MarkD833/Arduino-SP0256-Shield/code/vocab_v1.1.asm

;====================================================================
; Arduino SP0256-AL2 Shield Project
; https://github.com/MarkD833/Arduino-SP0256-Shield
;====================================================================
; This is the lookup table that will provide the starting address
; in the EEPROM for the sequence of allophones required to speak
; the word or phrase.
;
; They are arranged with 5 words per row just to make it easier to
; count!
;
; The vocabulary is split into evenly spaced blocks of words so that
; all words starting with the same letter are grouped in the same block.
;
; For example, to speak the word DANGER, the index number is 751 and
; to speak the word INCHES, the index number is 2004.
;
; Feel free to alter the spacing but as it stands, you can have up to
; 250 words or phrases in each block.
;====================================================================

; 

;====================================================================
; Edit this text string to hold whatever identifier you want
;
VERSION_STR EQU "SP0256 Vocabulary v1.1"

    ORG 0000
    DW  VERSTR
    
; Words starting with A - index starts at 1

	DW	A,ABLE,ABORT,ABORTED,AC
	DW	ACCUMULATE,ACKNOWLEDGE,ACTIVATE,ACTIVATING,ACTIVE
	DW	ACTIVITY,ADD,ADDRESS,ADJUST,AFTER
	DW	AGAIN,AIR,AISLE,ALARM,ALERT
	DW	ALL,ALTERNATE,AM1,AM2,AMP
	DW	AMPERE,AN,AND,ANNOUNCEMENT,ANSWER
	DW	APRIL,ARRIVAL,ASK,ASSISTANCE,ASTERN
	DW	AT,ATTENTION,AUGUST,AUTHORIZE,AUTO
	DW	AVAILABLE,AVERAGE,AWAY

; Words starting with B - index starts at 250
	ORG	500
    DW	B,BACK,BAROMETRIC,BASEMENT,BATH
	DW	BATTERY,BEEN,BEFORE,BETWEEN,BIN
	DW	BLACK,BLOCKING,BLUE,BRAKE,BUDGET
	DW	BUDGETING,BUILDING,BUOY,BUSY,BUTTON
	DW	BUY,BY
	
; Words starting with C - index starts at 500
	ORG	1000
	DW	C,CALENDAR,CALL,CANCEL,CAPACITANCE
	DW	CAR,CASE,CAUTION,CEASE,CELSIUS
	DW	CENT,CENTI,CENTIGRADE,CENTIMETER,CHANGE
	DW	CHANNEL,CHECK,CHECKED,CHECKING,CIRCUIT
	DW	CLEAR,CLOCK,CLOSE,CLOSED,CODE
	DW	COLD,COLLIDE,COMMA,COMMAND,COMMON
	DW	COMMUNICATION,COMPLETE,COMPUTER,CONDITION,CONFIGURATION
	DW	CONNECT,CONTINUE,CONTROL,CONVERTER,COOKIE
	DW	COOL,COPY,CORRECT,COST,COUNT
	DW	CROSS,CUSTOMER,CUT,CUTTING
	
; Words starting with D - index starts at 750
	ORG	1500
	DW	D,DANGER,DATA,DATE,DAY
	DW	DC,DECEMBER,DECREASE,DEFAULT,DEGREE
	DW	DELAY,DEMONSTRATION,DEPOSIT,DEPTH,DIAL
	DW	DIALING,DID,DISABLE,DISABLED,DIVIDE
	DW	DOLLAR,DOOR,DOWN
	
; Words starting with E - index starts at 1000
	ORG	2000
	DW	E,EAST,EIGHT,EIGHTEEN,EIGHTY
	DW	ELECTRIC,ELECTRICITY,ELEVEN,ELSE,EMERGENCY
	DW	ENABLE,ENABLED,END,ENGAGE,ENTER
	DW	ENTRY,EQUAL,EQUALS,ERROR,ESCAPE
	DW	EVACUATE,EXAMINE,EXIT,EXTREME
	
; Words starting with F - index starts at 1250
	ORG	2500
	DW	F,FAIL,FAILED,FAILURE,FAR
	DW	FARAD,FAST,FASTER,FEBRUARY,FEET
	DW	FIFTEEN,FIFTH,FIFTY,FIGHT,FIRE
	DW	FIRST,FIVE,FLOOR,FLOW,FORTY
	DW	FORWARD,FOUR,FOURTEEN,FRIDAY,FROM
	DW	FRONTAL,FUEL,FUSE,FUSED
	
; Words starting with G - index starts at 1500
	ORG	3000
	DW	G,GALLON,GAS,GET,GO
	DW	GOING,GOOD,GRAM,GRAY,GREAT
	DW	GREATER,GREEN,GROUP
	
; Words starting with H - index starts at 1750
	ORG	3500
	DW	H,HALF,HAVE,HELLO,HELP
	DW	HERE,HERTZ,HIGH,HIGHER,HIRE
	DW	HIT,HOLD,HOME,HOUR,HOUSE
	DW	HUNDRED,HURT
	
; Words starting with I - index starts at 2000
	ORG	4000
	DW	I,IF,IN,INACTIVE,INCHES
	DW	INCORPORATED,INCORRECT,INCREASE,INSERT,INTERFACE
	DW	INTRUDER,INVALID,INVESTIGATE,IS,IT
	
; Words starting with J - index starts at 2250
	ORG	4500
	DW	J,JANUARY,JULY,JUNE,JUST
	
; Words starting with K - index starts at 2500
	ORG	5000
	DW	K,KEY,KEYPAD,KILO
	
; Words starting with L - index starts at 2750
	ORG	5500
	DW	L,LEAVE,LEFT,LESS,LESSER
	DW	LEVEL,LIE,LIGHT,LIME,LIMIT
	DW	LINE,LINK,LISTEN,LOAD,LOCK
	DW	LOCKED,LOOP,LOOPED,LOW,LOWER
	
; Words starting with M - index starts at 3000
	ORG	6000
	DW	M,MARCH,MARK,MAY,MEGA
	DW	MEMORY,MESSAGE,METER,MICRO,MILE
	DW	MILLI,MILLIMETER,MILLION,MINUS,MINUTE
	DW	MISS,MISSING,MODEL,MODEM,MODULE
	DW	MONDAY,MONITOR,MORE,MOVE,MY
	
; Words starting with N - index starts at 3250
	ORG	6500
	DW	N,NANO,NEAR,NEED,NEXT
	DW	NIGHT,NINE,NINETEEN,NINETY,NO
	DW	NORMAL,NORTH,NOT,NOTICE,NOVEMBER
	DW	NUMBER
	
; Words starting with O - index starts at 3500
	ORG	7000
	DW	O,OCLOCK,OCTOBER,OF,OFF
	DW	OHM,OKAY,ON,ONE,ONWARD
	DW	OPEN,OPERATOR,OPTICAL,OR_,OTHER
	DW	OUT,OVER,OVER_RANGE
	
; Words starting with P - index starts at 3750
	ORG	7500
	DW	P,PAIR,PAN,PARENTHESIS,PASS
	DW	PASSED,PAST,PER,PERCENT,PHONE
	DW	PHONE_NUMBER,PHYSICAL,PICO,PLACE,PLAY
	DW	PLEASE,PLUS,PM,POINT,POUND
	DW	POWER,PRESENT,PRESS,PRESSURE,PROGRAM
	DW	PULL,PULSE,PULSES,PUSH,PUT
	
; Words starting with Q - index starts at 4000
	ORG	8000
	DW	Q,QUARTER
	
; Words starting with R - index starts at 4250
	ORG	8500
	DW	R,RAIN,RANGE,RATE,RE
	DW	REACH,READY,RECEIVED,RECEIVER,RECORD
	DW	RED,REMOVE,REPAIR,REPEAT,REPLACE
	DW	RESET,RESISTANCE,RESPONSE,RESTORE,RESTORED
	DW	RETURN,REVERSE,RIGHT,RING,ROBOT
	DW	ROOM,ROUTE,RUN,RUNNING
	
; Words starting with S - index starts at 4500
	ORG	9000
	DW	S,SAFE,SATURDAY,SCORE,SECOND
	DW	SECURE,SECURITY,SEE,SELECT,SEND
	DW	SENSOR,SENT,SEPTEMBER,SEQUENCE,SERVICE
	DW	SET,SEVEN,SEVENTEEN,SEVENTY,SHORT
	DW	SHOULD,SIDE,SIGHT,SINK,SITE
	DW	SIX,SIXTEEN,SIXTY,SLOW,SLOWER
	DW	SMILE,SMOKE,SOUND,SOUTH,SPACE
	DW	SPAN,SPARE,SPEED,SPEAK,SPELL
	DW	SQUAD,STAIR,STAR,START,STARTING
	DW	STATION,STATUS,STEAM,STERN,STOP
	DW	STOPPED,STOPPING,STORE,STORM,STREAM
	DW	STREET,SUB,SUBSCRIBER,SUNDAY,SUPERVISORY
	DW	SWITCH,SWITCHED,SYSTEM
	
; Words starting with T - index starts at 4750
	ORG	9500
	DW	T,TALK,TALKING,TANK,TAPE
	DW	TAPING,TARGET,TEA,TEAR,TEEN
	DW	TEMPERATURE,TEMPORARY,TEN,TERMINATE,TERMINATED
	DW	TEST,THAN,THANK,THANKYOU,THAT
	DW	THE,THEE,THEN,THERE,THERM
	DW	THERMAL,THIRD,THIRTEEN,THIRTY,THIS
	DW	THOUSAND,THREE,THURSDAY,TIDE,TIME
	DW	TIP,TODAY,TONE,TOTAL,TOUCH
	DW	TRACKING,TRAFFIC,TRANSFER,TRIP,TRUE
	DW	TRUNK,TRY,TUESDAY,TURN,TWELVE
	DW	TWENTY,TWO,TYPE
	
; Words starting with U - index starts at 5000
	ORG	10000
	DW	U,UN,UNABLE,UNATTENDED,UNIT
	DW	UNKNOWN,UNLOCK,UNLOCKED,UNTRUE,UP
	DW	USE,USED,UTILITY
	
; Words starting with V - index starts at 5250
	ORG	10500
	DW	V,VOICE,VOLT,VOLTAGE,VOTE
	
; Words starting with W - index starts at 5500
	ORG	11000
	DW	W,WAIT,WAITING,WAKE,WAKEUP
	DW	WARM,WARNING,WAS,WATER,WATT
	DW	WAVE,WEAR,WEDNESDAY,WEEK,WELCOME
	DW	WEST,WHAT,WILL,WIND1,WIND2
	DW	WISH,WITH,WITHIN,WORD,WORK
	DW	WORKING
	
; Words starting with X - index starts at 5750
	ORG	11500
	DW	X,XRAY
	
; Words starting with Y - index starts at 6000
	ORG	12000
	DW	Y,YELLOW,YES,YOU,YOUR
	
; Words starting with Z - index starts at 6250
	ORG	12500
	DW	Z,ZERO,ZONE

;====================================================================
; Version string from the start of this file will get stored here
;====================================================================
VERSTR:
    DB  VERSION_STR,0
    
;====================================================================
; These are the sequences of allophones needed to create the sound
; of each individual word. Make sure to end each sequence with 0xFF
;
; The words (i.e. labels) do not need to be in alphabetical order. 
;====================================================================

A:		DB	PA2,EY,PA3,0xFF
ABLE:		DB	PA2,EY,PA2,BB2,EL,PA3,0xFF
ABORT:		DB	PA2,AX,PA2,BB2,OR,PA3,TT2,PA3,0xFF
ABORTED:		DB	PA2,AX,PA2,BB2,OR,PA3,TT2,IH,PA2,DD1,PA3,0xFF
AC:		DB	PA2,EY,PA3,SS,SS,IY,PA3,0xFF		; Alternating Current
ACCUMULATE:		DB	PA2,AE,PA3,KK1,YY1,UW1,MM,YY1,UW1,LL,EY,PA3,TT2,PA3,0xFF
ACKNOWLEDGE:		DB	PA2,AE,PA3,KK2,NN1,OW,LL,EH,PA2,JH,PA3,0xFF
ACTIVATE:		DB	PA2,AE,PA3,KK1,PA3,TT2,IH,VV,EY,PA3,TT2,PA3,0xFF
ACTIVATING:		DB	PA2,AE,PA3,KK1,PA3,TT2,IH,VV,EY,PA3,TT2,IH,NG,PA3,0xFF
ACTIVE:		DB	PA2,AE,PA3,KK1,PA3,TT2,IH,VV,PA3,0xFF
ACTIVITY:		DB	PA2,AE,PA3,KK1,PA3,TT2,IH,VV,IH,PA3,TT2,IY,PA3,0xFF
ADD:		DB	PA2,AE,AE,PA2,DD1,PA3,0xFF
ADDRESS:		DB	PA2,AE,PA2,DD2,RR2,EH,SS,PA3,0xFF
ADJUST:		DB	PA2,AE,PA2,JH,AX,SS,SS,PA3,TT2,PA3,0xFF
AFTER:		DB	PA2,AE,FF,PA3,TT2,ER1,PA3,0xFF
AGAIN:		DB	PA2,AX,PA2,GG1,EH,EH,NN1,PA3,0xFF
AIR:		DB	PA2,EH,XR,PA3,0xFF
AISLE:		DB	PA2,AY,EL,PA3,0xFF
ALARM:		DB	PA2,AX,LL,AR,MM,PA3,0xFF
ALERT:		DB	PA2,AX,LL,ER1,PA3,TT2,PA3,0xFF
ALL:		DB	PA2,AO,LL,PA3,0xFF
ALTERNATE:		DB	PA2,AO,LL,PA3,TT2,ER1,NN1,EY,PA3,TT2,PA3,0xFF
AM1:		DB	PA2,AE,MM,PA3,0xFF			; AM - as in I AM
AM2			DB	PA2,EY,PA3,EH,EH,MM,PA3,0xFF	; A.M. - time
AMP:		DB	PA2,AE,MM,PA1,PP,PA3,0xFF
AMPERE:		DB	PA2,AE,MM,PA3,PP,ER1,PA3,0xFF
AN:		DB	PA2,AE,NN1,PA3,0xFF
AND:		DB	PA2,AE,NN1,PA2,DD1,PA3,0xFF
ANNOUNCEMENT:		DB	PA2,AE,NN1,AW,NN1,SS,SS,MM,IH,NN1,PA3,TT2,PA3,0xFF
ANSWER:		DB	PA2,AE,NN1,SS,SS,ER1,PA3,0xFF
APRIL:		DB	PA2,AX,PA3,PP,RR2,IH,LL,PA3,0xFF
ARRIVAL:		DB	PA2,AX,RR2,AY,VV,EL,PA3,0xFF
ASK:		DB	PA2,AE,SS,SS,PA3,KK2,PA3,0xFF
ASSISTANCE:		DB	PA2,AE,SS,SS,IH,SS,SS,PA3,TT2,AE,NN1,SS,SS,PA3,0xFF
ASTERN:		DB	PA2,AE,SS,SS,PA3,TT2,ER1,PA2,NN1,PA3,0xFF
AT:		DB	PA2,AE,PA3,TT2,PA3,0xFF
ATTENTION:		DB	PA2,AE,PA3,TT2,EH,NN1,SH,AX,NN1,PA3,0xFF
AUGUST:		DB	PA2,AO,PA2,GG2,AX,SS,SS,PA3,TT2,PA3,0xFF
AUTHORIZE:		DB	PA2,AO,TH,ER1,AY,PA2,ZZ,PA3,0xFF
AUTO:		DB	PA2,AO,PA3,TT2,OW,PA3,0xFF
AVAILABLE:		DB	PA2,AX,VV,EY,LL,AX,PA2,BB2,EL,PA3,0xFF
AVERAGE:		DB	PA2,AX,VV,ER1,IH,PA2,JH,PA3,0xFF
AWAY:		DB	PA2,AX,WW,EY,PA3,0xFF
B:		DB	PA2,BB2,IY,PA3,0xFF
BACK:		DB	PA2,BB2,AE,PA3,KK2,PA3,0xFF
BAROMETRIC:		DB	PA2,BB2,XR,AX,MM,EH,PA3,TT2,RR2,IH,PA3,KK2,PA3,0xFF
BASEMENT:		DB	PA2,BB2,EY,SS,MM,IH,NN1,PA3,TT2,PA3,0xFF
BATH:		DB	PA2,BB2,AE,TH,PA3,0xFF
BATTERY:		DB	PA2,BB2,AE,PA3,TT2,ER1,IY,PA3,0xFF
BEEN:		DB	PA2,BB2,IY,NN1,PA3,0xFF
BEFORE:		DB	PA2,BB2,IY,FF,OR,PA3,0xFF
BETWEEN:		DB	PA2,BB2,IY,TT2,WW,IY,NN1,PA3,0xFF
BIN:		DB	PA2,BB2,IH,NN1,PA3,0xFF
BLACK:		DB	PA2,BB1,LL,AE,PA3,KK2,PA3,0xFF
BLOCKING:		DB	PA2,BB1,LL,AA,PA3,KK1,IH,NG,PA3,0xFF
BLUE:		DB	PA2,BB1,LL,UW2,PA3,0xFF
BRAKE:		DB	PA2,BB1,RR2,EY,PA3,KK1,PA3,0xFF
BUDGET:		DB	PA2,BB2,AX,PA2,JH,EH,PA3,TT2,PA3,0xFF
BUDGETING:		DB	PA2,BB2,AX,PA2,JH,EH,PA3,TT2,IH,NG,PA3,0xFF
BUILDING:		DB	PA2,BB2,IH,IH,LL,PA2,DD2,IH,NG,PA3,0xFF
BUOY:		DB	PA2,BB2,OY,PA3,0xFF
BUSY:		DB	PA2,BB2,IH,ZZ,IY,PA3,0xFF
BUTTON:		DB	PA2,BB2,AX,PA3,TT2,AX,NN1,PA3,0xFF
BUY:		DB	PA2,BB2,AY,PA3,0xFF
BY:		DB	PA2,BB2,AY,PA3,0xFF
C:		DB	PA2,SS,SS,IY,PA3,0xFF
CALENDAR:	DB	PA2,KK1,AE,LL,EH,NN1,PA2,DD2,ER1,PA3,0XFF
CALL:		DB	PA2,KK1,AO,LL,PA3,0xFF
CANCEL:		DB	PA2,KK1,AE,NN1,SS,SS,EL,PA3,0xFF
CAPACITANCE:		DB	PA2,KK1,AE,PA3,PP,AE,SS,SS,IH,PA3,TT2,AE,NN1,SS,SS,PA3,0xFF
CAR:		DB	PA2,KK3,AR,PA3,0xFF
CASE:		DB	PA2,KK1,EY,SS,PA3,0xFF
CAUTION:		DB	PA2,KK1,AO,SH,AX,NN1,PA3,0xFF
CEASE:		DB	PA2,SS,SS,IY,ZZ,PA3,0xFF
CELSIUS:		DB	PA2,SS,SS,EH,LL,SS,SS,IH,AX,ZZ,PA3,0xFF
CENT:		DB	PA2,SS,SS,EH,NN1,PA3,TT2,PA3,0xFF
CENTI:		DB	PA2,SS,SS,EH,NN1,PA3,TT2,IY,PA3,0xFF
CENTIGRADE:		DB	PA2,SS,SS,EH,NN1,PA3,TT2,IH,PA2,GG2,RR2,EY,PA2,DD2,PA3,0xFF
CENTIMETER:		DB	PA2,SS,SS,EH,NN1,PA3,TT2,IH,MM,IY,PA3,TT2,ER1,PA3,0xFF
CHANGE:		DB	PA2,CH,EY,NN1,PA2,JH,PA3,0xFF
CHANNEL:		DB	PA2,PA3,CH,AE,NN2,EL,PA3,0xFF
CHECK:		DB	PA2,CH,EH,PA3,KK2,PA3,0xFF
CHECKED:		DB	PA2,CH,EH,PA3,KK2,PA2,TT2,PA3,0xFF
CHECKING:		DB	PA2,CH,EH,PA3,KK1,IH,NG,PA3,0xFF
CIRCUIT:		DB	PA2,SS,SS,ER2,PA3,KK3,IH,PA3,TT2,PA3,0xFF
CLEAR:		DB	PA2,KK1,LL,YR,PA3,0xFF
CLOCK:		DB	PA2,KK1,LL,AA,PA3,KK2,PA3,0xFF
CLOSE:		DB	PA2,KK1,LL,OW,ZZ,PA3,0xFF
CLOSED:		DB	PA2,KK1,LL,OW,ZZ,DD2,PA3,0xFF
CODE:		DB	PA2,KK3,OW,PA2,DD2,PA3,0xFF
COLD:		DB	PA2,KK3,OW,LL,PA2,DD2,PA3,0xFF
COLLIDE:	DB	KK3,AX,LL,AY,DD1,PA3,0xFF
COMMA:		DB	PA2,KK3,AA,MM,ER2,PA3,0xFF
COMMAND:		DB	PA2,KK3,AA,MM,AE,NN1,PA2,DD1,PA3,0xFF
COMMON:		DB	PA2,KK3,AA,MM,AX,NN1,PA3,0xFF
COMMUNICATION:		DB	PA2,KK3,AA,MM,YY2,UW1,NN1,IH,PA3,KK1,EY,SH,AX,NN1,PA3,0xFF
COMPLETE:		DB	PA2,KK3,AA,MM,PA3,PP,LL,IY,PA3,TT2,PA3,0xFF
COMPUTER:		DB	KK3,AA,MM,PP,YY1,UW1,TT2,ER2,PA3,0xFF
CONDITION:		DB	PA2,KK3,AX,NN1,PA2,DD2,IH,SH,AX,NN1,PA3,0xFF
CONFIGURATION:		DB	PA2,KK3,AX,NN1,FF,IH,PA2,GG2,YY1,UW1,ER1,EY,SH,AX,NN1,PA3,0xFF
CONNECT:		DB	PA2,KK3,AX,NN1,EH,PA3,KK1,PA3,TT2,PA3,0xFF
CONTINUE:		DB	PA2,KK3,AX,NN1,PA3,TT2,IH,NN1,YY1,UW1,PA3,0xFF
CONTROL:		DB	PA2,KK3,AX,NN1,PA3,TT2,RR2,AO,LL,PA3,0xFF
CONVERTER:		DB	PA2,KK3,AX,NN1,VV,ER1,PA3,TT2,ER1,PA3,0xFF
COOKIE:			DB	KK3,UH,KK1,IY,PA3,0xFF
COOL:		DB	PA2,KK3,UW2,LL,PA3,0xFF
COPY:		DB	PA2,KK3,AA,PA3,PP,IY,PA3,0xFF
CORRECT:		DB	PA2,KK3,OR,RR2,EH,PA3,KK1,PA3,TT2,PA3,0xFF
COST:		DB	PA2,KK3,AA,SS,SS,PA3,TT2,PA3,0xFF
COUNT:		DB	PA2,KK3,AW,NN1,PA3,TT2,PA3,0xFF
CROSS:		DB	PA2,KK1,RR2,AO,AO,SS,SS,PA3,0xFF
CUSTOMER:		DB	PA2,KK3,AX,SS,SS,PA3,TT2,AX,MM,ER1,PA3,0xFF
CUT:		DB	PA2,KK3,AX,PA3,TT2,PA3,0xFF
CUTTING:		DB	PA2,KK3,AX,PA3,TT2,IH,NG,PA3,0xFF
D:		DB	PA2,DD2,IY,PA3,0xFF
DANGER:		DB	PA2,DD2,EY,NN1,PA2,JH,ER1,PA3,0xFF
DATA:		DB	PA2,DD2,AE,PA3,TT2,AX,PA3,0xFF
DATE:		DB	PA2,DD2,EY,PA3,TT2,PA3,0xFF
DAY:		DB	PA2,DD2,EY,PA3,0xFF
DC:		DB	PA2,DD2,IY,PA3,SS,IY,PA3,0xFF
DECEMBER:		DB	PA2,DD2,IH,SS,SS,EH,MM,BB1,ER1,PA3,0xFF
DECREASE:		DB	PA2,DD2,IH,PA3,KK1,RR2,IY,ZZ,PA3,0xFF
DEFAULT:		DB	PA2,DD2,IH,FF,AO,LL,PA3,TT2,PA3,0xFF
DEGREE:		DB	PA2,DD2,IH,PA2,GG2,RR2,IY,PA3,0xFF
DELAY:		DB	PA2,DD2,IH,LL,EY,PA3,0xFF
DEMONSTRATION:		DB	PA2,DD2,IH,MM,AA,NN1,SS,SS,PA3,TT2,RR2,EY,SH,AX,NN1,PA3,0xFF
DEPOSIT:		DB	PA2,DD2,IH,PA3,PP,AA,ZZ,IH,PA3,TT2,PA3,0xFF
DEPTH:		DB	PA2,DD2,EH,PA3,PP,TH,PA3,0xFF
DIAL:		DB	PA2,DD2,AY,AE,LL,PA3,0xFF
DIALING:		DB	PA2,DD2,AY,AE,LL,IH,NG,PA3,0xFF
DID:		DB	PA2,DD2,IH,PA2,DD1,PA3,0xFF
DISABLE:		DB	PA2,DD2,IH,SS,EY,PA2,BB2,EL,PA3,0xFF
DISABLED:		DB	PA2,DD2,IH,SS,EY,PA2,BB2,EL,PA2,DD1,PA3,0xFF
DIVIDE:		DB	PA2,DD2,IH,VV,AY,PA2,DD2,PA3,0xFF
DOLLAR:		DB	PA2,DD2,AA,LL,ER1,PA3,0xFF
DOOR:		DB	PA2,DD2,OR,PA3,0xFF
DOWN:		DB	PA2,DD2,AW,NN1,PA3,0xFF
E:		DB	PA2,IY,PA3,0xFF
EAST:		DB	PA2,IY,SS,SS,PA3,TT2,PA3,0xFF
EIGHT:		DB	PA2,EY,PA3,TT2,PA3,0xFF
EIGHTEEN:		DB	PA2,EY,PA3,TT2,IY,NN1,PA3,0xFF
EIGHTY:		DB	PA2,EY,PA3,TT2,IY,PA3,0xFF
ELECTRIC:		DB	PA2,EH,LL,EH,PA3,KK1,PA3,TT2,RR2,IH,PA3,KK2,PA3,0xFF
ELECTRICITY:		DB	PA2,EH,LL,EH,PA3,KK1,PA3,TT2,RR2,IH,SS,SS,IH,PA3,TT2,IY,PA3,0xFF
ELEVEN:		DB	PA2,EH,LL,EH,VV,EH,NN1,PA3,0xFF
ELSE:		DB	PA2,EH,LL,SS,SS,PA3,0xFF
EMERGENCY:		DB	PA2,EH,MM,ER1,PA2,JH,EH,NN1,SS,SS,IY,PA3,0xFF
ENABLE:		DB	PA2,EH,NN1,EY,PA2,BB2,EL,PA3,0xFF
ENABLED:		DB	PA2,EH,NN1,EY,PA2,BB2,EL,PA2,DD1,PA3,0xFF
END:		DB	PA2,EH,NN1,PA2,DD1,PA3,0xFF
ENGAGE:		DB	PA2,EH,EH,NN1,GG1,EY,PA2,JH,PA3,0xFF
ENTER:		DB	PA2,EH,NN1,PA3,TT2,ER1,PA3,0xFF
ENTRY:		DB	PA2,EH,NN1,PA3,TT2,RR2,IY,PA3,0xFF
EQUAL:		DB	PA2,IY,PA2,PA3,KK3,WH,AX,EL,PA3,0xFF
EQUALS:		DB	PA2,IY,PA2,PA3,KK3,WH,AX,EL,ZZ,PA3,0xFF
ERROR:		DB	PA2,EH,RR2,ER1,PA3,0xFF
ESCAPE:		DB	PA2,EH,SS,SS,PA3,KK1,EY,PA3,PP,PA3,0xFF
EVACUATE:		DB	PA2,IY,VV,AE,PA3,KK2,YY1,UW1,EY,PA3,TT2,PA3,0xFF
EXAMINE:		DB	PA2,EH,PA3,KK2,SS,AE,MM,IH,NN1,PA3,0xFF
EXIT:		DB	PA2,EH,PA3,KK2,SS,IH,PA3,TT2,PA3,0xFF
EXTREME:		DB	PA2,EH,PA3,KK2,SS,PA3,TT2,RR2,IY,MM,PA3,0xFF
F:		DB	PA2,EH,EH,FF,PA3,0xFF
FAIL:		DB	PA2,FF,EY,LL,PA3,0xFF
FAILED:		DB	PA2,FF,EY,LL,PA2,DD1,PA3,0xFF
FAILURE:		DB	PA2,FF,EY,LL,UW1,ER1,PA3,0xFF
FAR:		DB	PA2,FF,AR,PA3,0xFF
FARAD:		DB	PA2,FF,XR,AE,PA2,DD1,PA3,0xFF
FAST:		DB	PA2,FF,AE,SS,SS,PA3,TT2,PA3,0xFF
FASTER:		DB	PA2,FF,AE,SS,SS,PA3,TT2,ER1,PA3,0xFF
FEBRUARY:		DB	PA2,FF,EH,PA2,BB2,RR2,UW2,XR,IY,PA3,0xFF
FEET:		DB	PA2,FF,IY,PA3,TT2,PA3,0xFF
FIFTEEN:		DB	PA2,FF,IH,FF,PA3,TT2,IY,NN1,PA3,0xFF
FIFTH:		DB	PA2,FF,IH,FF,TH,PA3,0xFF
FIFTY:		DB	PA2,FF,IH,FF,PA3,TT2,IY,PA3,0xFF
FIGHT:		DB	PA2,FF,AY,PA3,TT2,PA3,0xFF
FIRE:		DB	PA2,FF,AY,ER1,PA3,0xFF
FIRST:		DB	PA2,FF,ER2,SS,SS,PA3,TT2,PA3,0xFF
FIVE:		DB	PA2,FF,AY,VV,PA3,0xFF
FLOOR:		DB	PA2,FF,LL,OR,PA3,0xFF
FLOW:		DB	PA2,FF,LL,OW,PA3,0xFF
FORTY:		DB	PA2,FF,OR,PA3,TT2,IY,PA3,0xFF
FORWARD:		DB	PA2,FF,OR,WW,AA,DD2,PA3,0xFF
FOUR:		DB	PA2,FF,OR,PA3,0xFF
FOURTEEN:		DB	PA2,FF,OR,PA3,TT2,IY,NN1,PA3,0xFF
FRIDAY:		DB	PA2,FF,RR2,AY,PA2,DD2,EY,PA3,0xFF
FROM:		DB	PA2,FF,RR2,AA,MM,PA3,0xFF
FRONTAL:		DB	PA2,FF,RR2,AX,NN1,PA3,TT2,EL,PA3,0xFF
FUEL:		DB	PA2,FF,YY1,UW1,LL,PA3,0xFF
FUSE:		DB	PA2,FF,YY1,UW1,ZZ,PA3,0xFF
FUSED:		DB	PA2,FF,YY1,UW1,ZZ,PA2,DD2,PA3,0xFF
G:		DB	PA2,PA2,JH,IY,PA3,0xFF
GALLON:		DB	PA2,GG2,AE,LL,AX,NN1,PA3,0xFF
GAS:		DB	PA2,GG2,AE,ZZ,PA3,0xFF
GET:		DB	PA2,GG1,EH,PA3,TT2,PA3,0xFF
GO:		DB	PA2,GG2,OW,PA3,0xFF
GOING:		DB	PA2,GG2,OW,IH,NG,PA3,0xFF
GOOD:		DB	PA2,GG2,UH,PA2,DD1,PA3,0xFF
GRAM:		DB	PA2,GG2,RR2,AE,MM,PA3,0xFF
GRAY:		DB	PA2,GG2,RR2,EY,PA3,0xFF
GREAT:		DB	PA2,GG3,RR2,EY,TT2,PA3,0xFF
GREATER:		DB	PA2,GG3,RR2,EY,TT2,ER1,PA3,0xFF
GREEN:		DB	PA2,GG2,RR2,IY,NN1,PA3,0xFF
GROUP:		DB	PA2,GG2,RR2,UW2,PA3,PP,PA3,0xFF
H:		DB	PA2,EY,PA3,CH,PA3,0xFF
HALF:		DB	PA2,HH2,AR,FF,PA3,0xFF
HAVE:		DB	PA2,HH1,AE,VV,PA3,0xFF
HELLO:		DB	PA2,HH1,EH,LL,OW,PA3,0xFF
HELP:		DB	PA2,HH1,EH,LL,PA3,PP,PA3,0xFF
HERE:		DB	PA2,HH1,YR,PA3,0xFF
HERTZ:		DB	PA2,HH1,ER1,PA3,TT2,ZZ,PA3,0xFF
HIGH:		DB	PA2,HH1,AY,PA3,0xFF
HIGHER:		DB	PA2,HH1,AY,ER1,PA3,0xFF
HIRE:		DB	PA2,HH1,AY,ER1,PA3,0xFF
HIT:		DB	PA2,HH1,IH,PA3,TT2,PA3,0xFF
HOLD:		DB	PA2,HH2,OW,LL,PA2,DD1,PA3,0xFF
HOME:		DB	PA2,HH2,OW,MM,PA3,0xFF
HOUR:		DB	PA2,AW,ER1,PA3,0xFF
HOUSE:		DB	PA2,HH2,AW,SS,PA3,0xFF
HUNDRED:		DB	PA2,HH2,AX,NN1,PA2,DD2,RR2,PA2,DD1,PA3,0xFF
HURT:		DB	PA2,HH2,ER1,PA3,TT2,PA3,0xFF
I:		DB	PA2,AY,PA3,0xFF
IF:		DB	PA2,IH,FF,PA3,0xFF
IN:		DB	PA2,IH,NN1,PA3,0xFF
INACTIVE:		DB	PA2,IH,NN1,AE,PA3,KK1,PA3,TT2,IH,VV,PA3,0xFF
INCHES:		DB	PA2,IH,NN1,PA3,CH,SS,PA3,0xFF
INCORPORATED:		DB	PA2,IH,NN1,PA3,KK3,OR,PA3,PP,OR,EY,PA3,TT2,IH,PA2,DD1,PA3,0xFF
INCORRECT:		DB	PA2,IH,NN1,PA3,KK3,OR,RR2,EH,PA3,KK1,PA3,TT2,PA3,0xFF
INCREASE:		DB	PA2,IH,NN1,PA3,KK1,RR2,IY,ZZ,PA3,0xFF
INSERT:		DB	PA2,IH,NN1,SS,SS,ER1,PA3,TT2,PA3,0xFF
INTERFACE:		DB	PA2,IH,NN1,PA3,TT2,ER1,FF,EY,SS,SS,PA3,0xFF
INTRUDER:		DB	PA2,IH,NN1,PA3,TT2,RR2,UW2,PA2,DD2,ER1,PA3,0xFF
INVALID:		DB	PA2,IH,NN1,VV,AE,LL,IH,PA2,DD1,PA3,0xFF
INVESTIGATE:	DB	PA2,IH,IH,NN1,VV,EH,EH,SS,PA2,PA3,TT2,IH,PA1,GG1,EY,PA2,TT2,PA3,0xFF
IS:		DB	PA2,IH,ZZ,PA3,0xFF
IT:		DB	PA2,IH,PA3,TT2,PA3,0xFF
J:		DB	PA2,PA2,JH,EY,PA3,0xFF
JANUARY:		DB	PA2,JH,AE,NN1,YY2,XR,IY,PA3,0xFF
JULY:		DB	PA2,JH,UW1,LL,AY,PA3,0xFF
JUNE:		DB	PA2,JH,UW2,NN1,PA3,0xFF
JUST:		DB	PA2,JH,AX,SS,SS,PA3,TT2,PA3,0xFF
K:		DB	PA2,KK1,EY,PA3,0xFF
KEY:		DB	PA2,KK1,IY,PA3,0xFF
KEYPAD:		DB	PA2,KK1,IY,PA3,PP,AE,PA2,DD1,PA3,0xFF
KILO:		DB	PA2,KK1,IH,LL,OW,PA3,0xFF
L:		DB	PA2,EH,EH,LL,PA3,0xFF
LEAVE:		DB	PA2,LL,IY,VV,PA3,0xFF
LEFT:		DB	PA2,LL,EH,FF,PA3,TT2,PA3,0xFF
LESS:		DB	PA2,LL,EH,SS,SS,PA3,0xFF
LESSER:		DB	PA2,LL,EH,SS,SS,ER1,PA3,0xFF
LETTER:		DB	PA2,LL,EH,EH,PA3,TT2,ER1,PA3,0xFF
LEVEL:		DB	PA2,LL,EH,VV,EL,PA3,0xFF
LIE:		DB	PA2,LL,AY,PA3,0xFF
LIGHT:		DB	PA2,LL,AY,PA3,TT2,PA3,0xFF
LIME:		DB	PA2,LL,AY,MM,PA3,0xFF
LIMIT:		DB	PA2,LL,IH,MM,IH,PA3,TT2,PA3,0xFF
LINE:		DB	PA2,LL,AY,NN1,PA3,0xFF
LINK:		DB	PA2,LL,IH,NG,PA3,KK2,PA3,0xFF
LISTEN:		DB	PA2,LL,IH,SS,SS,EH,NN1,PA3,0xFF
LOAD:		DB	PA2,LL,OW,PA2,DD1,PA3,0xFF
LOCK:		DB	PA2,LL,AA,PA3,KK2,PA3,0xFF
LOCKED:		DB	PA2,LL,AA,PA3,KK1,PA3,TT2,PA3,0xFF
LOOP:		DB	PA2,LL,UW2,PA3,PP,PA3,0xFF
LOOPED:		DB	PA2,LL,UW2,PA3,PP,PA3,TT2,PA3,0xFF
LOW:		DB	PA2,LL,OW,PA3,0xFF
LOWER:		DB	PA2,LL,OW,ER1,PA3,0xFF
M:		DB	PA2,EH,EH,MM,PA3,0xFF
MARCH:		DB	PA2,MM,AR,PA3,CH,PA3,0xFF
MARK:		DB	PA2,MM,AR,PA3,KK2,PA3,0xFF
MAY:		DB	PA2,MM,EY,PA3,0xFF
MEGA:		DB	PA2,MM,EH,PA2,GG2,AX,PA3,0xFF
MEMORY:		DB	PA2,MM,EH,EH,MM,ER2,IY,PA3,0xFF
MESSAGE:		DB	PA2,MM,EH,SS,SS,IH,PA2,JH,PA3,0xFF
METER:		DB	PA2,MM,IY,PA3,TT2,ER1,PA3,0xFF
MICRO:		DB	PA2,MM,AY,PA3,KK1,RR2,OW,PA3,0xFF
MILE:		DB	PA2,MM,AY,EL,PA3,0xFF
MILLI:		DB	PA2,MM,IH,LL,IY,PA3,0xFF
MILLIMETER:		DB	PA2,MM,IH,LL,IH,MM,IY,PA3,TT2,ER1,PA3,0xFF
MILLION:		DB	PA2,MM,IH,LL,IY,AX,NN1,PA3,0xFF
MINUS:		DB	PA2,MM,AY,NN2,UH,SS,PA3,0xFF
MINUTE:		DB	PA2,MM,IH,NN1,IH,PA3,TT2,PA3,0xFF
MISS:		DB	PA2,MM,IH,SS,PA3,0xFF
MISSING:		DB	PA2,MM,IH,SS,SS,IH,NG,PA3,0xFF
MODEL:		DB	PA2,MM,AA,PA2,DD2,EL,PA3,0xFF
MODEM:		DB	PA2,MM,OW,PA2,DD2,EH,MM,PA3,0xFF
MODULE:		DB	PA2,MM,AA,PA2,DD2,UW2,EL,PA3,0xFF
MONDAY:		DB	PA2,MM,AX,NN1,PA2,DD2,EY,PA3,0xFF
MONITOR:		DB	PA2,MM,AA,NN1,IH,PA3,TT2,ER1,PA3,0xFF
MORE:		DB	PA2,MM,OR,PA3,0xFF
MOVE:		DB	PA2,MM,UW2,VV,PA3,0xFF
MY:		DB	PA2,MM,AY,PA3,0xFF
N:		DB	PA2,EH,EH,NN1,PA3,0xFF
NANO:		DB	PA2,NN2,AE,PA2,NN2,OW,PA3,0xFF
NEAR:		DB	PA2,NN2,YR,PA3,0xFF
NEED:		DB	PA2,NN2,IY,PA2,DD1,PA3,0xFF
NEXT:		DB	PA2,NN2,EH,PA3,KK2,SS,PA3,TT2,PA3,0xFF
NIGHT:		DB	PA2,NN2,AY,PA3,TT2,PA3,0xFF
NINE:		DB	PA2,NN2,AY,NN1,PA3,0xFF
NINETEEN:		DB	PA2,NN2,AY,NN1,PA3,TT2,IY,NN1,PA3,0xFF
NINETY:		DB	PA2,NN2,AY,NN1,PA3,TT2,IY,PA3,0xFF
NO:		DB	PA2,NN2,OW,PA3,0xFF
NORMAL:		DB	PA2,NN2,OR,MM,EL,PA3,0xFF
NORTH:		DB	PA2,NN2,OR,TH,PA3,0xFF
NOT:		DB	PA2,NN2,AA,PA3,TT2,PA3,0xFF
NOTICE:		DB	PA2,NN2,OW,PA3,TT2,IH,SS,SS,PA3,0xFF
NOVEMBER:		DB	PA2,NN2,AX,VV,EH,MM,BB1,ER1,PA3,0xFF
NUMBER:		DB	PA2,NN2,AX,MM,ER1,PA3,0xFF
O:		DB	PA2,OW,PA3,0xFF
OCLOCK:		DB	PA2,OW,PA3,KK1,LL,AA,PA3,KK2,PA3,0xFF
OCTOBER:		DB	PA2,AA,PA3,KK1,PA3,TT2,OW,PA2,BB2,ER1,PA3,0xFF
OF:		DB	PA2,OW,VV,PA3,0xFF
OFF:		DB	PA2,AO,FF,FF,PA3,0xFF
OHM:		DB	PA2,OW,MM,PA3,0xFF
OKAY:		DB	PA2,OW,PA3,KK1,EY,PA3,0xFF
ON:		DB	PA2,AA,NN1,PA3,0xFF
ONE:		DB	PA2,WW,AX,NN1,PA3,0xFF
ONWARD:		DB	PA2,AA,NN1,WW,OR,PA2,DD1,PA3,0xFF
OPEN:		DB	PA2,OW,PA3,PP,EH,NN1,PA3,0xFF
OPERATOR:		DB	PA2,AA,PA3,PP,ER1,EY,PA3,TT2,ER1,PA3,0xFF
OPTICAL:		DB	PA2,AA,PA3,PP,PA3,TT2,IH,PA3,KK1,EL,PA3,0xFF
OR_:		DB	PA2,OR,PA3,0xFF
OTHER:		DB	PA2,AX,DH2,ER1,PA3,0xFF
OUT:		DB	PA2,AW,PA3,TT2,PA3,0xFF
OVER:		DB	PA2,OW,VV,ER1,PA3,0xFF
OVER_RANGE:		DB	PA2,OW,VV,ER1,PA1,RR1,EY,NN1,PA2,JH,PA3,0xFF
P:		DB	PA2,PP,IY,PA3,0xFF
PAIR:		DB	PA2,PP,EH,XR,PA3,0xFF
PAN:		DB	PA2,PP,AE,NN1,PA3,0xFF
PARENTHESIS:		DB	PA2,PP,XR,EH,NN1,TH,EH,ZZ,IH,SS,PA3,0xFF
PASS:		DB	PA2,PP,AE,SS,PA3,0xFF
PASSED:		DB	PA2,PP,AE,SS,SS,PA3,TT2,PA3,0xFF
PAST:		DB	PA2,PP,AE,SS,SS,PA3,TT2,PA3,0xFF
PER:		DB	PA2,PP,ER1,PA3,0xFF
PERCENT:		DB	PA2,PP,ER1,SS,SS,EH,NN1,PA3,TT2,PA3,0xFF
PHONE:		DB	PA2,FF,OW,NN1,PA3,0xFF
PHONE_NUMBER:		DB	PA2,FF,OW,NN1,PA2,NN2,AX,MM,BB1,ER1,PA3,0xFF
PHYSICAL:	DB	PA2,FF,FF,IH,ZZ,IH,PA3,KK1,AX,EL,PA3,0xFF
PICO:		DB	PA2,PP,IY,PA3,KK3,OW,PA3,0xFF
PLACE:		DB	PA2,PP,LL,EY,SS,SS,PA3,0xFF
PLAY:		DB	PA2,PP,LL,EY,PA3,0xFF
PLEASE:		DB	PA2,PP,LL,IY,ZZ,PA3,0xFF
PLUS:		DB	PA2,PP,LL,AX,SS,PA3,0xFF
PM:		DB	PA2,PP,IY,PA3,EH,MM,PA3,0xFF
POINT:		DB	PA2,PP,OY,NN1,PA3,TT2,PA3,0xFF
POUND:		DB	PA2,PP,AW,NN1,PA2,DD1,PA3,0xFF
POWER:		DB	PA2,PP,AW,ER1,PA3,0xFF
PRESENT:		DB	PA2,PP,RR2,EH,ZZ,EH,NN1,PA3,TT2,PA3,0xFF
PRESS:		DB	PA2,PP,RR2,EH,SS,PA3,0xFF
PRESSURE:		DB	PA2,PP,RR2,EH,SH,ER1,PA3,0xFF
PROGRAM:		DB	PA2,PP,RR2,OW,PA2,GG2,RR2,AE,MM,PA3,0xFF
PULL:		DB	PA2,PP,UH,LL,PA3,0xFF
PULSE:		DB	PA2,PP,UH,LL,SS,SS,PA3,0xFF
PULSES:		DB	PA2,PP,UH,LL,SS,SS,IH,ZZ,PA3,0xFF
PUSH:		DB	PA2,PP,AX,SH,PA3,0xFF
PUT:		DB	PA2,PP,UH,PA3,TT2,PA3,0xFF
Q:		DB	PA2,KK1,YY1,UW2,PA3,0xFF
QUARTER:		DB	PA2,KK3,WH,OR,PA3,TT2,ER1,PA3,0xFF
R:		DB	PA2,AR,PA3,0xFF
RAIN:		DB	PA2,RR1,EY,NN1,PA3,0xFF
RANGE:		DB	PA2,RR1,EY,NN1,PA2,JH,PA3,0xFF
RATE:		DB	PA2,RR1,EY,PA3,TT2,PA3,0xFF
RE:		DB	PA2,RR1,IY,PA3,0xFF
REACH:		DB	PA2,RR1,IY,PA3,CH,PA3,0xFF
READY:		DB	PA2,RR1,EH,EH,PA1,DD1,IY,PA3,0xFF
RECEIVED:		DB	PA2,RR1,IY,SS,SS,IY,VV,PA2,DD1,PA3,0xFF
RECEIVER:		DB	PA2,RR1,IY,SS,SS,IY,VV,ER1,PA3,0xFF
RECORD:		DB	PA2,RR1,IY,PA3,KK3,OR,PA2,DD1,PA3,0xFF
RED:		DB	PA2,RR1,EH,PA2,DD1,PA3,0xFF
REMOVE:		DB	PA2,RR1,IY,MM,UW2,VV,PA3,0xFF
REPAIR:		DB	PA2,RR1,IY,PP,EH,XR,PA3,0xFF
REPEAT:		DB	PA2,RR1,IY,PP,IY,PA3,TT2,PA3,0xFF
REPLACE:		DB	PA2,RR1,IY,PP,LL,EY,SS,SS,PA3,0xFF
RESET:		DB	PA2,RR1,IY,SS,PA2,EH,PA3,TT2,PA3,0xFF
RESISTANCE:		DB	PA2,RR1,IY,ZZ,IH,SS,SS,PA3,TT2,AE,NN1,SS,SS,PA3,0xFF
RESPONSE:		DB	PA2,RR1,IY,SS,SS,PA3,PP,AA,NN1,SS,SS,PA3,0xFF
RESTORE:		DB	PA2,RR1,IY,SS,SS,PA3,TT2,OR,PA3,0xFF
RESTORED:		DB	PA2,RR1,IY,SS,SS,PA3,TT2,OR,PA2,DD1,PA3,0xFF
RETURN:		DB	PA2,RR1,IY,PA3,TT2,ER2,NN1,PA3,0xFF
REVERSE:		DB	PA2,RR1,IY,VV,ER2,SS,SS,PA3,0xFF
RIGHT:		DB	PA2,RR1,AY,PA3,TT2,PA3,0xFF
RING:		DB	PA2,RR1,IH,NG,PA3,0xFF
ROBOT:		DB	PA2,RR1,OW,PA2,BB2,AA,PA3,TT2,PA3,0xFF
ROOM:		DB	PA2,RR1,UW2,MM,PA3,0xFF
ROUTE:		DB	PA2,RR1,AW,PA3,TT2,PA3,0xFF
RUN:		DB	PA2,RR1,AX,NN1,PA3,0xFF
RUNNING:		DB	PA2,RR1,AX,NN1,IH,NG,PA3,0xFF
S:		DB	PA2,EH,EH,SS,SS,PA3,0xFF
SAFE:		DB	PA2,SS,SS,EY,FF,PA3,0xFF
SATURDAY:		DB	PA2,SS,SS,AE,PA3,TT2,ER1,PA2,DD2,EY,PA3,0xFF
SCORE:		DB	PA2,SS,SS,PA3,KK3,OR,PA3,0xFF
SECOND:		DB	PA2,SS,SS,EH,PA3,KK3,AX,NN1,PA2,DD1,PA3,0xFF
SECURE:		DB	PA2,SS,SS,EH,PA3,KK3,YY1,UW1,ER1,PA3,0xFF
SECURITY:		DB	PA2,SS,SS,EH,PA3,KK3,YY1,UW1,ER1,IH,PA3,TT2,IY,PA3,0xFF
SEE:		DB	PA2,SS,SS,IY,PA3,0xFF
SELECT:		DB	PA2,SS,SS,EH,LL,EH,PA3,KK1,PA3,TT2,PA3,0xFF
SEND:		DB	PA2,SS,SS,EH,NN1,PA2,DD1,PA3,0xFF
SENSOR:		DB	PA2,SS,SS,EH,NN1,SS,SS,ER1,PA3,0xFF
SENT:		DB	PA2,SS,SS,EH,NN1,PA3,TT2,PA3,0xFF
SEPTEMBER:		DB	PA2,SS,SS,EH,PA3,PP,PA3,TT2,EH,MM,BB1,ER1,PA3,0xFF
SEQUENCE:		DB	PA2,SS,SS,IY,PA3,KK3,WH,EH,NN1,SS,SS,PA3,0xFF
SERVICE:		DB	PA2,SS,SS,ER1,VV,IH,SS,SS,PA3,0xFF
SET:		DB	PA2,SS,SS,EH,PA3,TT2,PA3,0xFF
SEVEN:		DB	PA2,SS,SS,EH,VV,EH,NN1,PA3,0xFF
SEVENTEEN:		DB	PA2,SS,SS,EH,VV,EH,NN1,PA3,TT2,IY,NN1,PA3,0xFF
SEVENTY:		DB	PA2,SS,SS,EH,VV,EH,NN1,PA3,TT2,IY,PA3,0xFF
SHORT:		DB	PA2,SH,OR,PA3,TT2,PA3,0xFF
SHOULD:		DB	PA2,SH,UH,PA2,DD1,PA3,0xFF
SIDE:		DB	PA2,SS,SS,AY,PA2,DD2,PA3,0xFF
SIGHT:		DB	PA2,SS,SS,AY,PA3,TT2,PA3,0xFF
SINK:		DB	PA2,SS,SS,IH,NG,PA3,KK2,PA3,0xFF
SITE:		DB	PA2,SS,SS,AY,PA3,TT2,PA3,0xFF
SIX:		DB	PA2,SS,SS,IH,PA3,KK2,SS,PA3,0xFF
SIXTEEN:		DB	PA2,SS,SS,IH,PA3,KK2,SS,PA3,TT2,IY,NN1,PA3,0xFF
SIXTY:		DB	PA2,SS,SS,IH,PA3,KK2,SS,PA3,TT2,IY,PA3,0xFF
SLOW:		DB	PA2,SS,SS,LL,OW,PA3,0xFF
SLOWER:		DB	PA2,SS,SS,LL,OW,ER1,PA3,0xFF
SMILE:		DB	PA2,SS,SS,MM,AY,EL,PA3,0xFF
SMOKE:		DB	PA2,SS,SS,MM,OW,PA3,KK1,PA3,0xFF
SOUND:		DB	PA2,SS,SS,AW,NN1,PA2,DD1,PA3,0xFF
SOUTH:		DB	PA2,SS,SS,AW,TH,PA3,0xFF
SPACE:		DB	PA2,SS,SS,PA3,PP,EY,SS,SS,PA3,0xFF
SPAN:		DB	PA2,SS,SS,PA3,PP,AE,NN1,PA3,0xFF
SPARE:		DB	PA2,SS,SS,PA3,PP,XR,PA3,0xFF
SPEED:		DB	PA2,SS,SS,PA3,PP,IY,PA2,DD1,PA3,0xFF
SPEAK:		DB	PA2,SS,SS,PA3,PP,IY,PA3,KK2,PA3,0xFF
SPELL:		DB	PA2,SS,SS,PA3,PP,EH,LL,PA3,0xFF
SQUAD:		DB	PA2,SS,SS,PA3,KK3,WH,AA,PA2,DD1,PA3,0xFF
STAIR:		DB	PA2,SS,SS,PA3,TT2,EH,XR,PA3,0xFF
STAR:		DB	PA2,SS,SS,PA3,TT2,AR,PA3,0xFF
START:		DB	PA2,SS,SS,PA3,TT2,AR,PA3,TT2,PA3,0xFF
STARTING:	DB	PA2,SS,SS,PA3,TT2,AR,PA3,TT2,IH,NG,PA3,0xFF
STATION:		DB	PA2,SS,SS,PA3,TT2,EY,SH,AX,NN1,PA3,0xFF
STATUS:		DB	PA2,SS,SS,PA3,TT2,AE,PA3,TT2,AX,SS,PA3,0xFF
STEAM:		DB	PA2,SS,SS,PA3,TT2,IY,MM,PA3,0xFF
STERN:		DB	PA2,SS,SS,PA3,TT2,ER1,NN1,PA3,0xFF
STOP:		DB	PA2,SS,SS,PA3,TT1,AA,AA,PA3,PP,PA3,0xFF
STOPPED:	DB	PA2,SS,SS,PA3,TT1,AA,AA,PA3,PP,PA3,TT2,PA3,0xFF
STOPPING:	DB	PA2,SS,SS,PA3,TT1,AA,AA,PA3,PP,IH,NG,PA3,0xFF
STORE:		DB	PA2,SS,SS,PA3,TT2,OR,PA3,0xFF
STORM:		DB	PA2,SS,SS,PA3,TT2,OR,MM,PA3,0xFF
STREAM:		DB	PA2,SS,SS,PA3,TT2,RR2,IY,MM,PA3,0xFF
STREET:		DB	PA2,SS,SS,PA3,TT2,RR2,IY,PA3,TT2,PA3,0xFF
SUB:		DB	PA2,SS,SS,AX,PA2,BB1,PA3,0xFF
SUBSCRIBER:		DB	PA2,SS,SS,AX,PA2,BB1,SS,SS,PA3,KK1,RR2,AY,PA2,BB2,ER1,PA3,0xFF
SUNDAY:		DB	PA2,SS,SS,AX,NN1,PA2,DD2,EY,PA3,0xFF
SUPERVISORY:		DB	PA2,SS,SS,UW2,PA3,PP,ER1,VV,AY,ZZ,OR,IY,PA3,0xFF
SWITCH:		DB	PA2,SS,SS,WW,IH,IH,PA3,CH,PA3,0xFF
SWITCHED:		DB	PA2,SS,SS,WW,IH,IH,PA3,CH,PA3,TT2,PA3,0xFF
SYSTEM:		DB	PA2,SS,SS,IH,IH,SS,SS,PA3,TT2,EH,MM,PA3,0xFF
T:		DB	PA2,TT2,IY,PA3,0xFF
TALK		DB	PA2,TT2,AO,AO,PA2,KK2,PA3,0xFF
TALKING:	DB	PA2,TT2,AO,AO,PA2,KK1,IH,NG,PA3,0xFF
TANK:		DB	PA2,TT2,AE,NG,PA3,KK2,PA3,0xFF
TAPE:		DB	PA2,TT2,EY,PA3,PP,PA3,0xFF
TAPING:		DB	PA2,TT2,AE,PA3,PP,IH,NG,PA3,0xFF
TARGET:		DB	PA2,TT2,AR,PA2,GG1,EH,PA3,TT2,PA3,0xFF
TEA:		DB	PA2,TT2,IY,PA3,0xFF
TEAR:		DB	PA2,TT2,EH,XR,PA3,0xFF
TEEN:		DB	PA2,TT2,IY,NN1,PA3,0xFF
TEMPERATURE:		DB	PA2,TT2,EH,MM,PA3,PP,ER1,AE,PA3,CH,ER1,PA3,0xFF
TEMPORARY:		DB	PA2,TT2,EH,MM,PA3,PP,OR,XR,IY,PA3,0xFF
TEN:		DB	PA2,TT2,EH,NN1,PA3,0xFF
TERMINATE:		DB	PA2,TT2,ER1,MM,IH,NN1,EY,PA3,TT2,PA3,0xFF
TERMINATED:		DB	PA2,TT2,ER1,MM,IH,NN1,EY,PA3,TT2,IH,PA2,DD1,PA3,0xFF
TEST:		DB	PA2,TT2,EH,SS,SS,PA3,TT2,PA3,0xFF
THAN:		DB	PA2,DH1,AE,NN1,PA3,0xFF
THANK:		DB	PA2,TH,AE,NG,PA3,KK2,PA3,0xFF
THANKYOU:		DB	PA2,TH,AE,NG,PA3,KK2,PA2,YY2,UW2,PA3,0xFF
THAT:		DB	PA2,DH1,AE,PA3,TT2,PA3,0xFF
THE:		DB	PA2,DH1,AX,PA3,0xFF
THEE:		DB	PA2,TH,IY,PA3,0xFF
THEN:		DB	PA2,DH1,EH,NN1,PA3,0xFF
THERE:		DB	PA2,DH1,XR,PA3,0xFF
THERM:		DB	PA2,TH,ER1,MM,PA3,0xFF
THERMAL:		DB	PA2,TH,ER1,MM,EL,PA3,0xFF
THIRD:		DB	PA2,TH,ER2,PA2,DD1,PA3,0xFF
THIRTEEN:		DB	PA2,TH,ER2,PA3,TT2,IY,NN1,PA3,0xFF
THIRTY:		DB	PA2,TH,ER2,PA3,TT2,IY,PA3,0xFF
THIS:		DB	PA2,DH1,IH,SS,SS,PA3,0xFF
THOUSAND:		DB	PA2,TH,AW,ZZ,AE,NN1,PA2,DD1,PA3,0xFF
THREE:		DB	PA2,TH,RR2,IY,PA3,0xFF
THURSDAY:		DB	PA2,TH,ER1,SS,SS,PA2,DD2,EY,PA3,0xFF
TIDE:		DB	PA2,TT2,AY,PA2,DD2,PA3,0xFF
TIME:		DB	PA2,TT2,AY,MM,PA3,0xFF
TIP:		DB	PA2,TT2,IH,PA3,PP,PA3,0xFF
TODAY:		DB	PA2,TT2,UW2,DD2,EY,PA3,0xFF
TONE:		DB	PA2,TT2,OW,NN1,PA3,0xFF
TOTAL:		DB	PA2,TT2,OW,PA3,TT2,EL,PA3,0xFF
TOUCH:		DB	PA2,TT2,UH,PA3,CH,PA3,0xFF
TRACKING:		DB	PA2,TT2,RR2,AE,PA3,KK1,IH,NG,PA3,0xFF
TRAFFIC:		DB	PA2,TT2,RR2,AE,FF,IH,PA3,KK2,PA3,0xFF
TRANSFER:		DB	PA2,TT2,RR2,AE,NN1,SS,SS,FF,ER1,PA3,0xFF
TRIP:		DB	PA2,TT2,RR2,IH,PA3,PP,PA3,0xFF
TRUE:		DB	PA2,TT2,RR2,UW2,PA3,0xFF
TRUNK:		DB	PA2,TT2,RR2,AX,NG,PA3,KK2,PA3,0xFF
TRY:		DB	PA2,TT2,RR2,AY,PA3,0xFF
TUESDAY:		DB	PA2,TT2,UW2,SS,SS,PA2,DD2,EY,PA3,0xFF
TURN:		DB	PA2,TT2,ER1,NN1,PA3,0xFF
TWELVE:		DB	PA2,TT2,WW,EH,PA2,LL,VV,PA3,0xFF
TWENTY:		DB	PA2,TT2,WW,EH,NN1,PA3,TT2,IY,PA3,0xFF
TWO:		DB	PA2,TT2,UW2,PA3,0xFF
TYPE:		DB	PA2,TT2,AY,PA3,PP,PA3,0xFF
U:		DB	PA2,YY1,UW2,PA3,0xFF
UN:		DB	PA2,AX,NN1,PA3,0xFF
UNABLE:		DB	PA2,UH,NN1,NN1,PA1,EY,BB2,EL,PA3,0xFF
UNATTENDED:		DB	PA2,AX,NN1,AE,PA3,TT2,EH,NN1,PA2,DD2,IH,PA2,DD1,PA3,0xFF
UNIT:		DB	PA2,YY2,UW1,NN1,IH,PA3,TT2,PA3,0xFF
UNKNOWN:		DB	PA2,AX,NN1,PA3,NN2,OW,NN1,PA3,0xFF
UNLOCK:		DB	PA2,AX,NN1,LL,AA,PA3,KK2,PA3,0xFF
UNLOCKED:		DB	PA2,AX,NN1,LL,AA,PA3,KK1,PA3,TT2,PA3,0xFF
UNTRUE:		DB	PA2,AX,NN1,PA3,TT2,RR2,UW2,PA3,0xFF
UP:		DB	PA2,AX,PA3,PP,PA3,0xFF
USE:		DB	PA2,YY1,UW1,ZZ,PA3,0xFF
USED:		DB	PA2,YY1,UW1,ZZ,PA2,DD1,PA3,0xFF
UTILITY:		DB	PA2,YY1,UW1,PA3,TT2,IH,LL,IH,PA3,TT2,IY,PA3,0xFF
V:		DB	PA2,VV,IY,PA3,0xFF
VOICE:		DB	PA2,VV,OY,SS,SS,PA3,0xFF
VOLT:		DB	PA2,VV,AA,LL,PA3,TT2,PA3,0xFF
VOLTAGE:		DB	PA2,VV,AA,LL,PA3,TT2,IH,PA2,JH,PA3,0xFF
VOTE:		DB	PA2,VV,OW,PA3,TT2,PA3,0xFF
W:		DB	PA2,DD2,AX,PA2,BB2,EL,YY1,UW1,PA3,0xFF
WAIT:		DB	PA2,WW,EY,PA3,TT2,PA3,0xFF
WAITING:		DB	PA2,WW,EY,PA3,TT2,IH,NG,PA3,0xFF
WAKE:		DB	PA2,WW,EY,PA3,KK1,PA3,0xFF
WAKEUP:		DB	PA2,WW,EY,PA3,KK1,PA2,AX,PA3,PP,PA3,0xFF
WARM:		DB	PA2,WW,OR,MM,PA3,0xFF
WARNING:		DB	PA2,WW,OR,NN1,IH,NG,PA3,0xFF
WAS:		DB	PA2,WW,AX,ZZ,PA3,0xFF
WATER:		DB	PA2,WW,AO,AO,PA3,TT2,ER1,PA3,0xFF
WATT:		DB	PA2,WW,AO,AO,PA3,TT2,PA3,0xFF
WAVE:		DB	PA2,WW,EY,VV,PA3,0xFF
WEAR:		DB	PA2,WW,EH,XR,PA3,0xFF
WEDNESDAY:		DB	PA2,WW,EH,PA2,NN1,SS,PA2,DD2,EY,PA3,0xFF
WEEK:		DB	PA2,WW,IY,PA3,KK2,PA3,0xFF
WELCOME:		DB	PA2,WW,EH,LL,PA3,KK3,AX,MM,PA3,0xFF
WEST:		DB	PA2,WW,EH,SS,SS,PA3,TT2,PA3,0xFF
WHAT:		DB	PA2,WH,AA,PA3,TT2,PA3,0xFF
WILL:		DB	PA2,WW,IH,LL,PA3,0xFF
WIND1:		DB	PA2,WW,AY,NN1,PA2,DD1,PA3,0xFF		; Wind as in wind-up
WIND2:		DB	PA2,WW,IH,NN1,PA2,DD1,PA3,0xFF		; Wind - weather
WISH:		DB	PA2,WW,IH,SH,PA3,0xFF
WITH:		DB	PA2,WW,IH,TH,PA3,0xFF
WITHIN:		DB	PA2,WW,IH,TH,IH,NN1,PA3,0xFF
WORD:		DB	PA2,WW,ER1,PA2,DD1,PA3,0xFF
WORK:		DB	PA2,WW,ER1,PA3,KK2,PA3,0xFF
WORKING:		DB	PA2,WW,ER1,PA3,KK1,IH,NG,PA3,0xFF
X:		DB	PA2,EH,PA3,KK2,SS,PA3,0xFF
XRAY:		DB	PA2,EH,PA3,KK2,SS,RR2,EY,PA3,0xFF
Y:		DB	PA2,WW,AY,PA3,0xFF
YELLOW:		DB	PA2,YY2,EH,LL,OW,PA3,0xFF
YES:		DB	PA2,YY2,EH,SS,SS,PA3,0xFF
YOU:		DB	PA2,YY2,UW2,PA3,0xFF
YOUR:		DB	PA2,YY2,OR,PA3,0xFF
Z:		DB	PA2,ZZ,IY,PA3,0xFF
ZERO:		DB	PA2,IY,XR,OW,PA3,0xFF
ZONE:		DB	PA2,ZZ,OW,NN1,PA3,0xFF

;====================================================================
; These are the 64 allophones for the SP0256-AL2
; Leave this out the way at the end of the file
;====================================================================
PA1	EQU	00
PA2	EQU	01
PA3	EQU	02
PA4	EQU	03
PA5	EQU	04
OY	EQU	05
AY	EQU	06
EH	EQU	07
KK3	EQU	08
PP	EQU	09
JH	EQU	10
NN1	EQU	11
IH	EQU	12
TT2	EQU	13
RR1	EQU	14
AX	EQU	15
MM	EQU	16
TT1	EQU	17
DH1	EQU	18
IY	EQU	19
EY	EQU	20
DD1	EQU	21
UW1	EQU	22
AO	EQU	23
AA	EQU	24
YY2	EQU	25
AE	EQU	26
HH1	EQU	27
BB1	EQU	28
TH	EQU	29
UH	EQU	30
UW2	EQU	31
AW	EQU	32
DD2	EQU	33
GG3	EQU	34
VV	EQU	35
GG1	EQU	36
SH	EQU	37
ZH	EQU	38
RR2	EQU	39
FF	EQU	40
KK2	EQU	41
KK1	EQU	42
ZZ	EQU	43
NG	EQU	44
LL	EQU	45
WW	EQU	46
XR	EQU	47
WH	EQU	48
YY1	EQU	49
CH	EQU	50
ER1	EQU	51
ER2	EQU	52
OW	EQU	53
DH2	EQU	54
SS	EQU	55
NN2	EQU	56
HH2	EQU	57
OR	EQU	58
AR	EQU	59
YR	EQU	60
GG2	EQU	61
EL	EQU	62
BB2	EQU	63
